danielftsilva/TS-808-Replica/KiCad Project/Layout/3D view.png

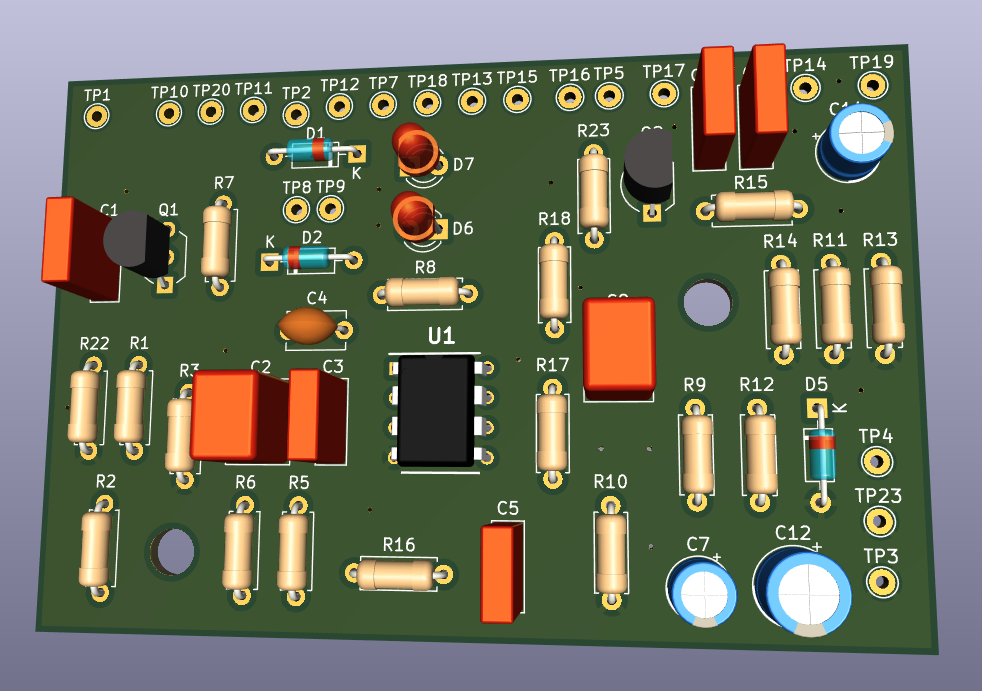
KiCad Project/Layout/3D view.png
