danielftsilva/TS-808-Replica/KiCad Project/Layout/Layout.png

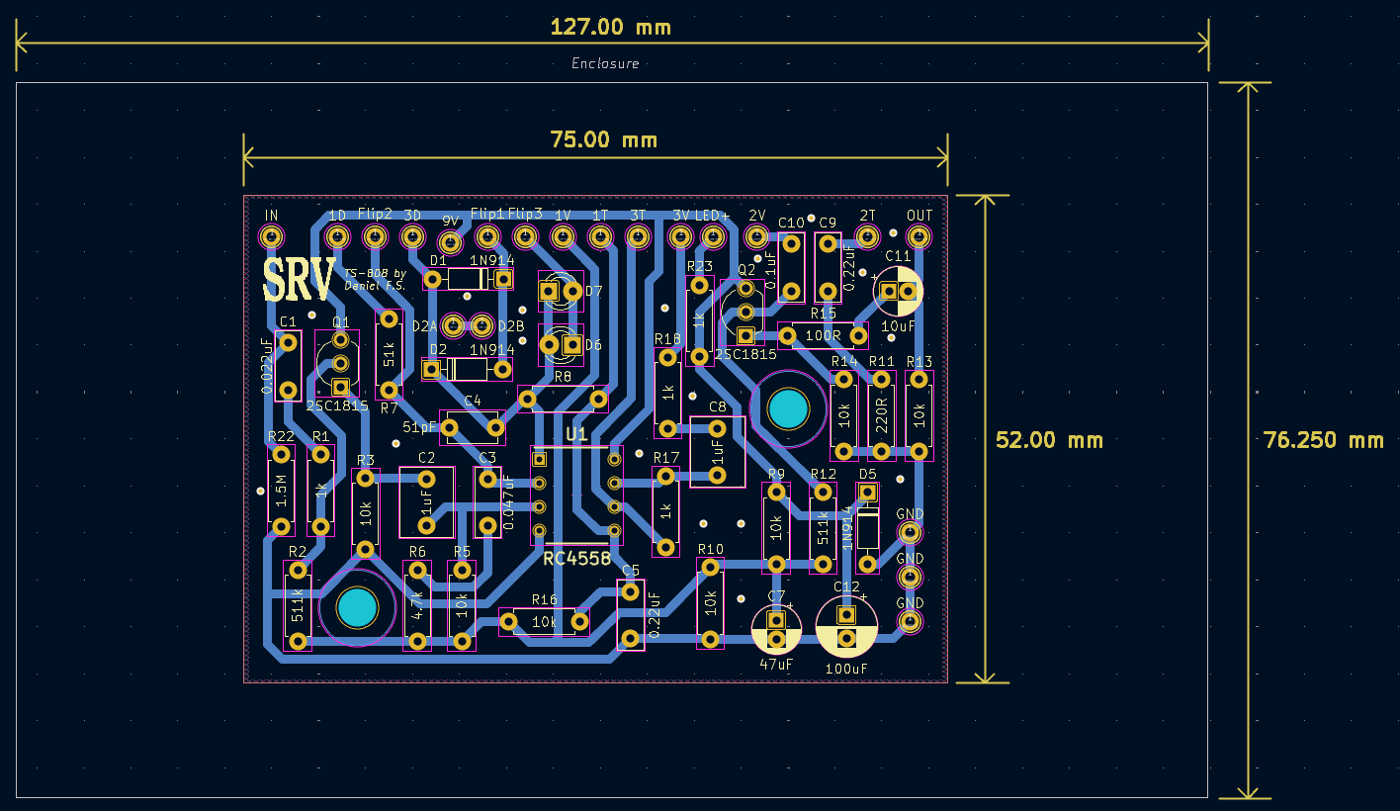
KiCad Project/Layout/Layout.png
