danielftsilva/TS-808-Replica/KiCad Project/Layout/Placement_1.png

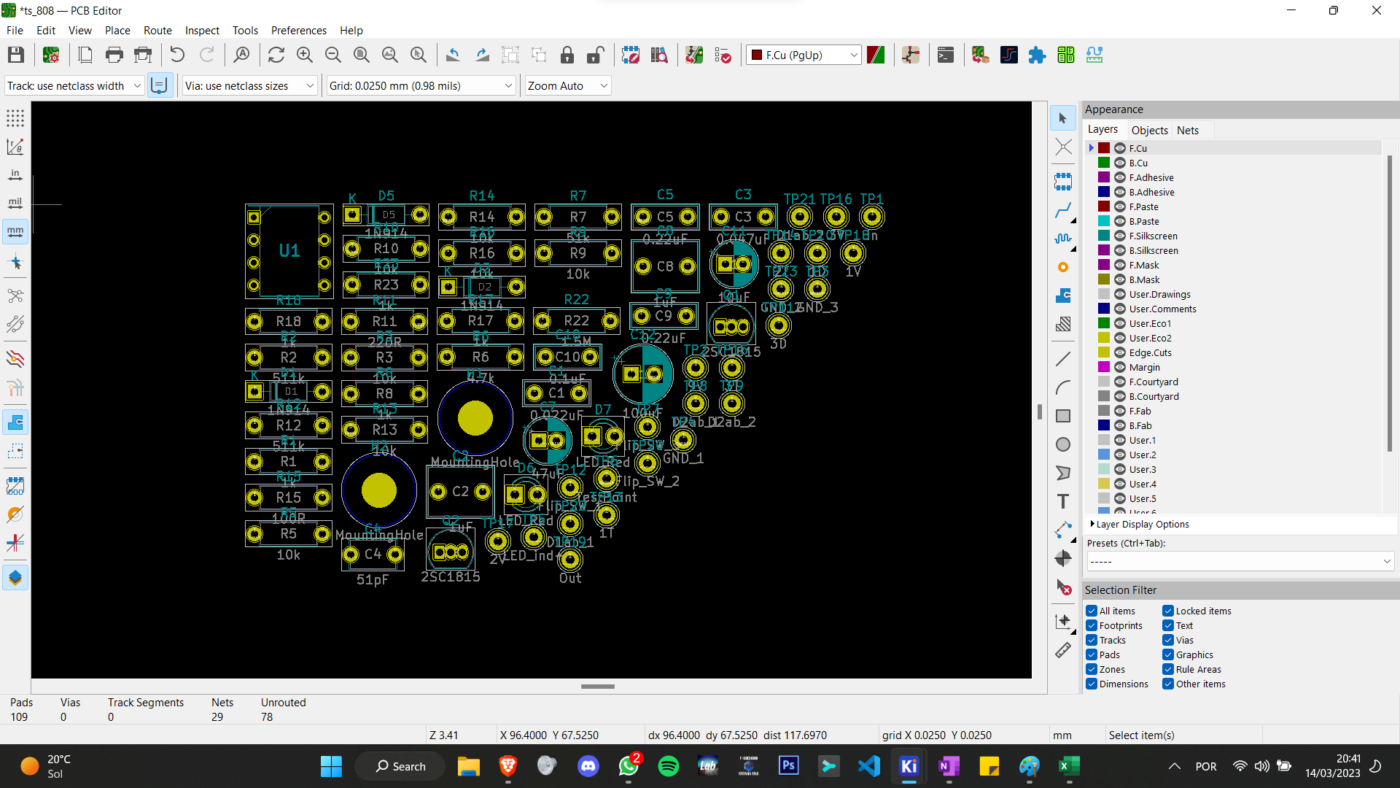
KiCad Project/Layout/Placement_1.png
