danielftsilva/TS-808-Replica/KiCad Project/Layout/Placement_2.png

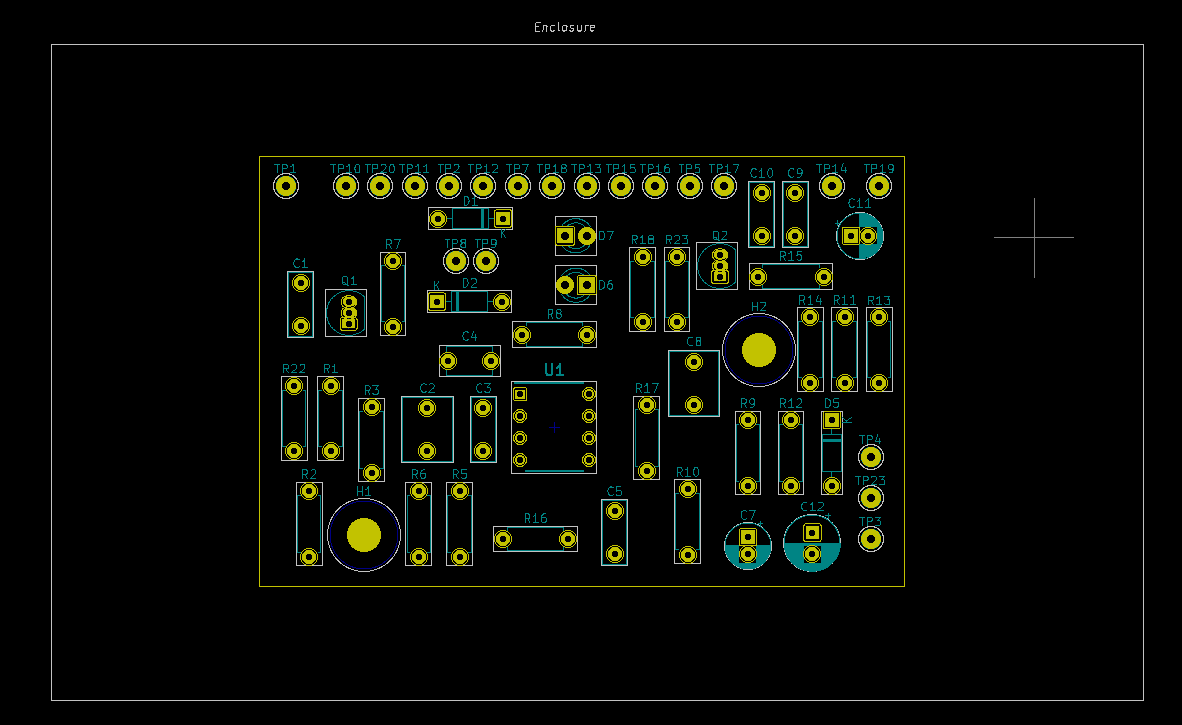
KiCad Project/Layout/Placement_2.png
