danielftsilva/TS-808-Replica/KiCad Project/Layout/tracks_1.png

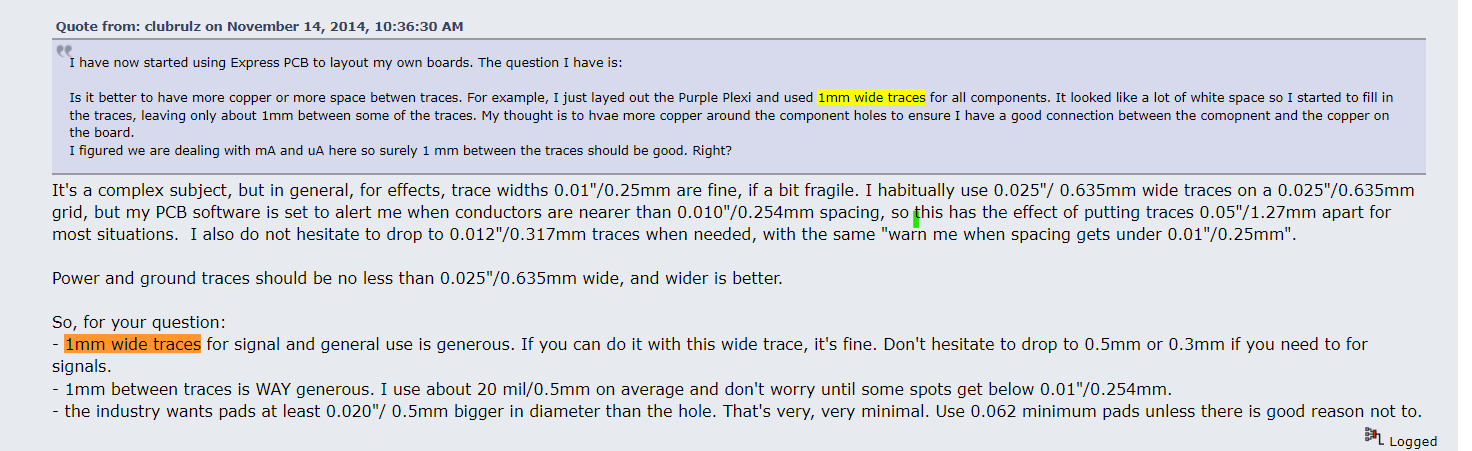
KiCad Project/Layout/tracks_1.png
