danielftsilva/TS-808-Replica/KiCad Project/Layout/tracks_2.png

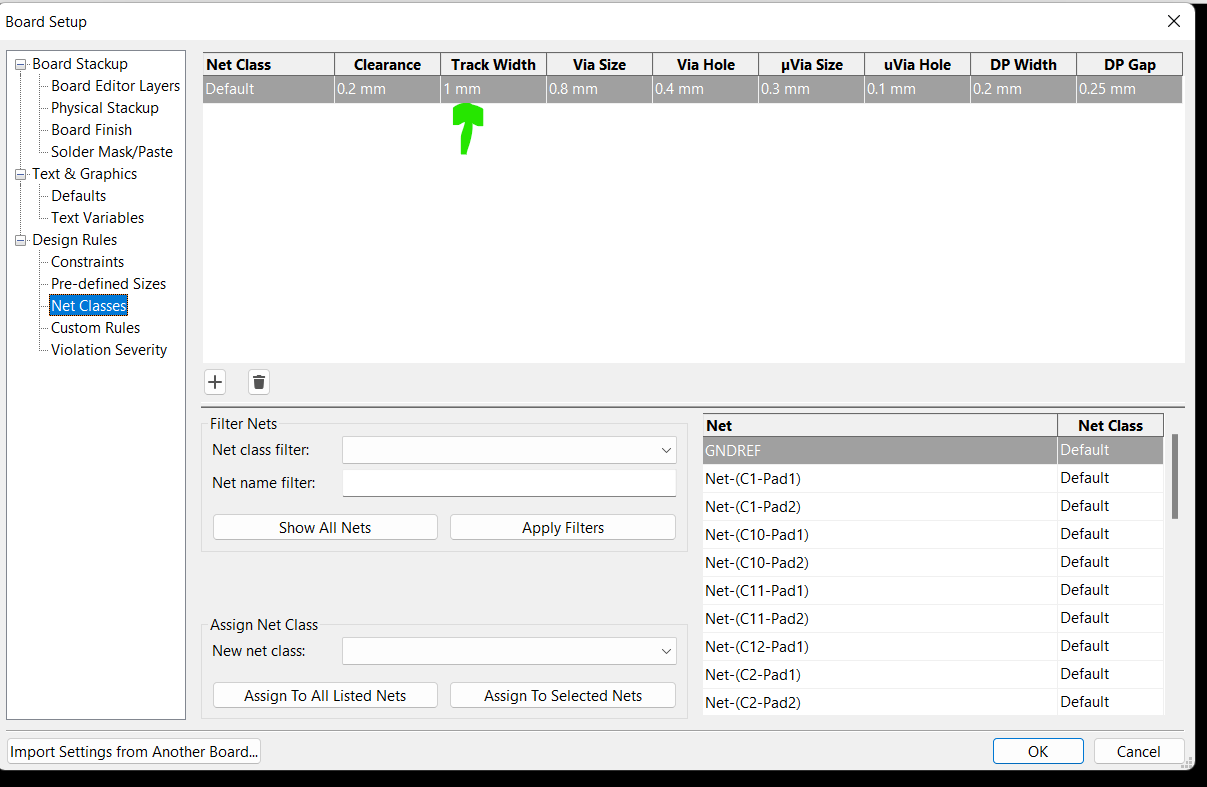
KiCad Project/Layout/tracks_2.png
