danielftsilva/TS-808-Replica/Assembly/PCB_populated.jpg

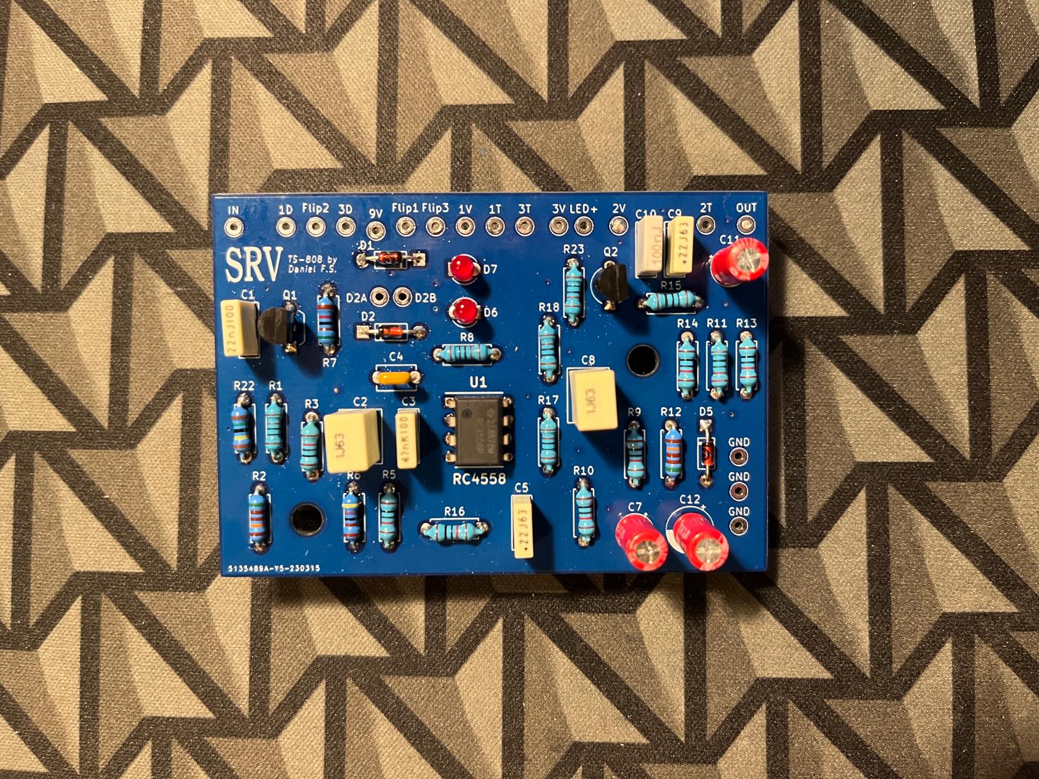
Assembly/PCB_populated.jpg
