danielftsilva/TS-808-Replica/Assembly/Pedal_assembled_2.jpeg

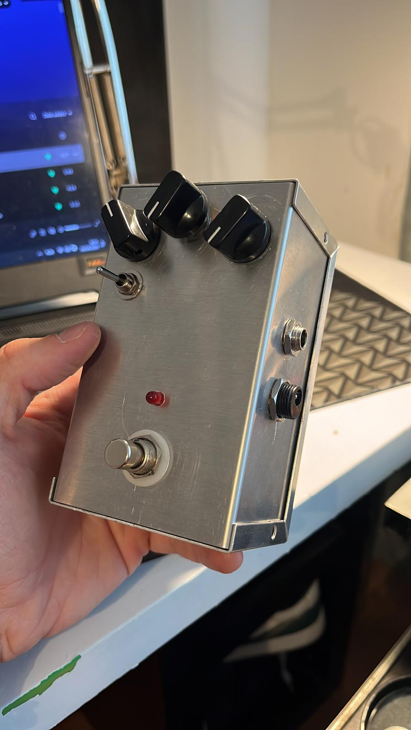
Assembly/Pedal_assembled_2.jpeg
