danielftsilva/TS-808-Replica/Assembly/Pedal_assembled_3.jpeg

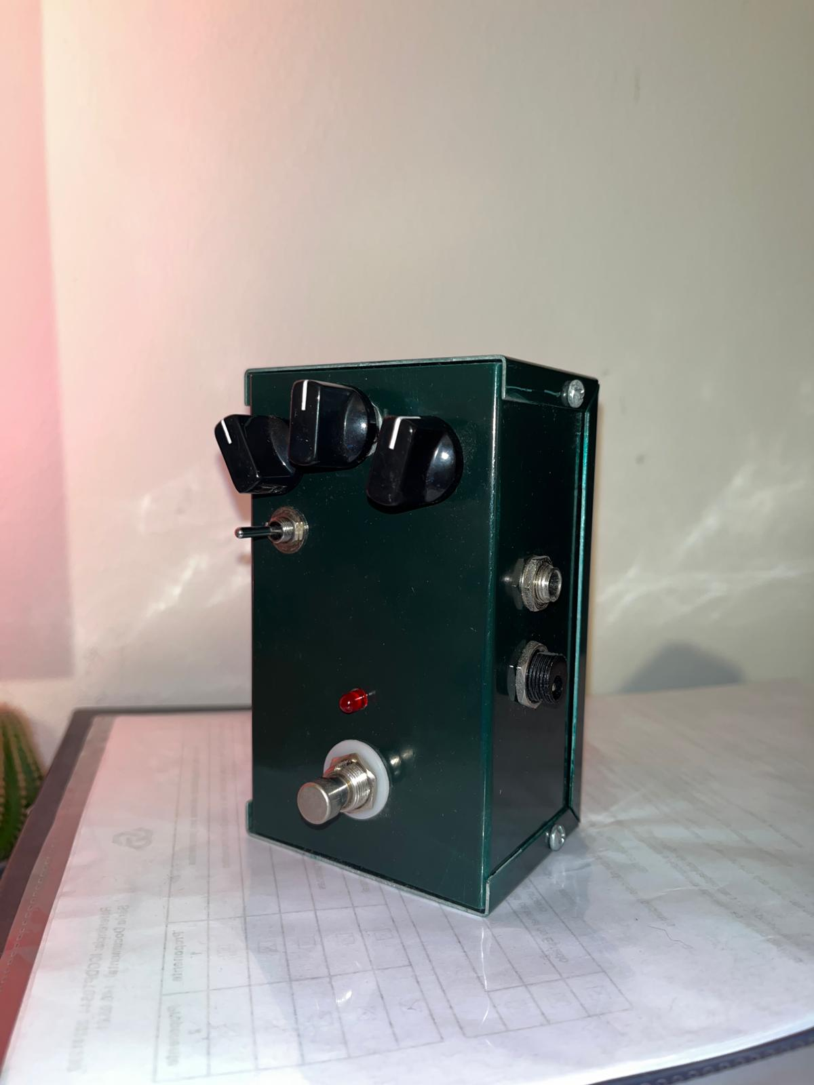
Assembly/Pedal_assembled_3.jpeg
