danielftsilva/TS-808-Replica/KiCad Project/production/JLCPCB_KiCad_board_setup_2.png

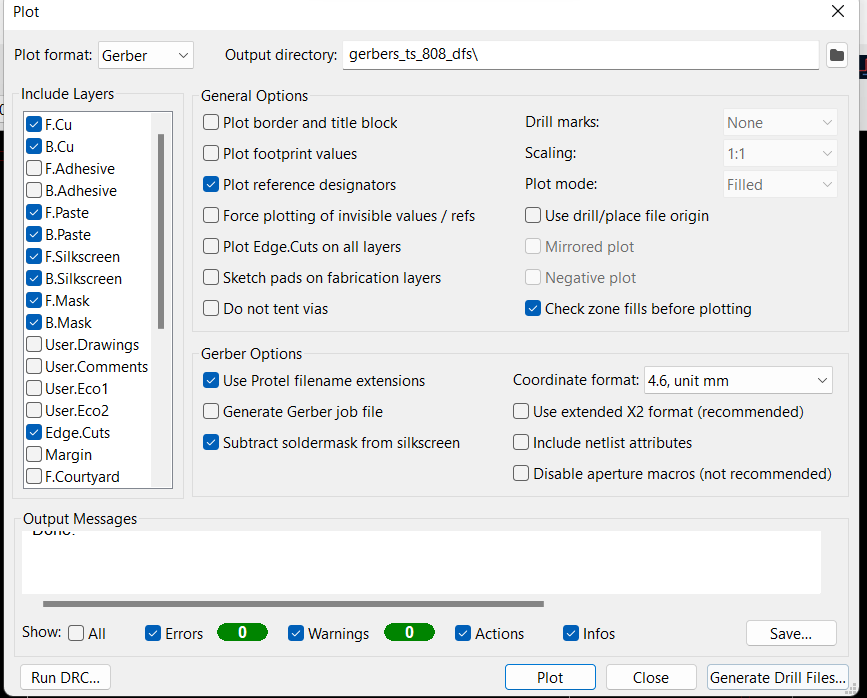
KiCad Project/production/JLCPCB_KiCad_board_setup_2.png
