danielftsilva/TS-808-Replica/Tests/Pedal_ON_1.jpeg

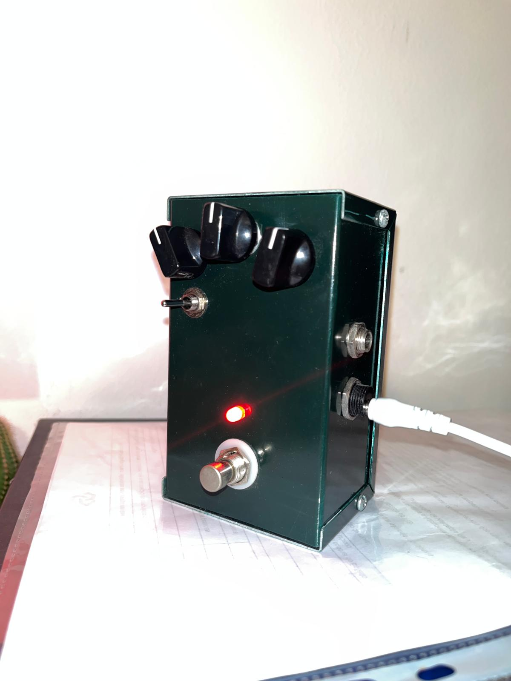
Tests/Pedal_ON_1.jpeg
