danielftsilva/TS-808-Replica/Tests/Pedal_ON_2.jpeg

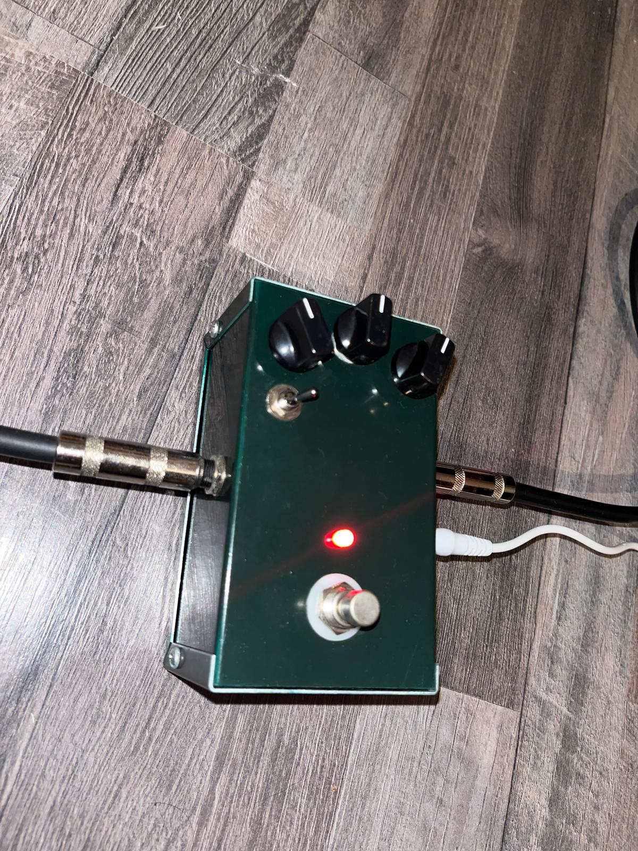
Tests/Pedal_ON_2.jpeg
