danielftsilva/TS-808-Replica/Tests/TROUBLESHOOTING CHART.jpg

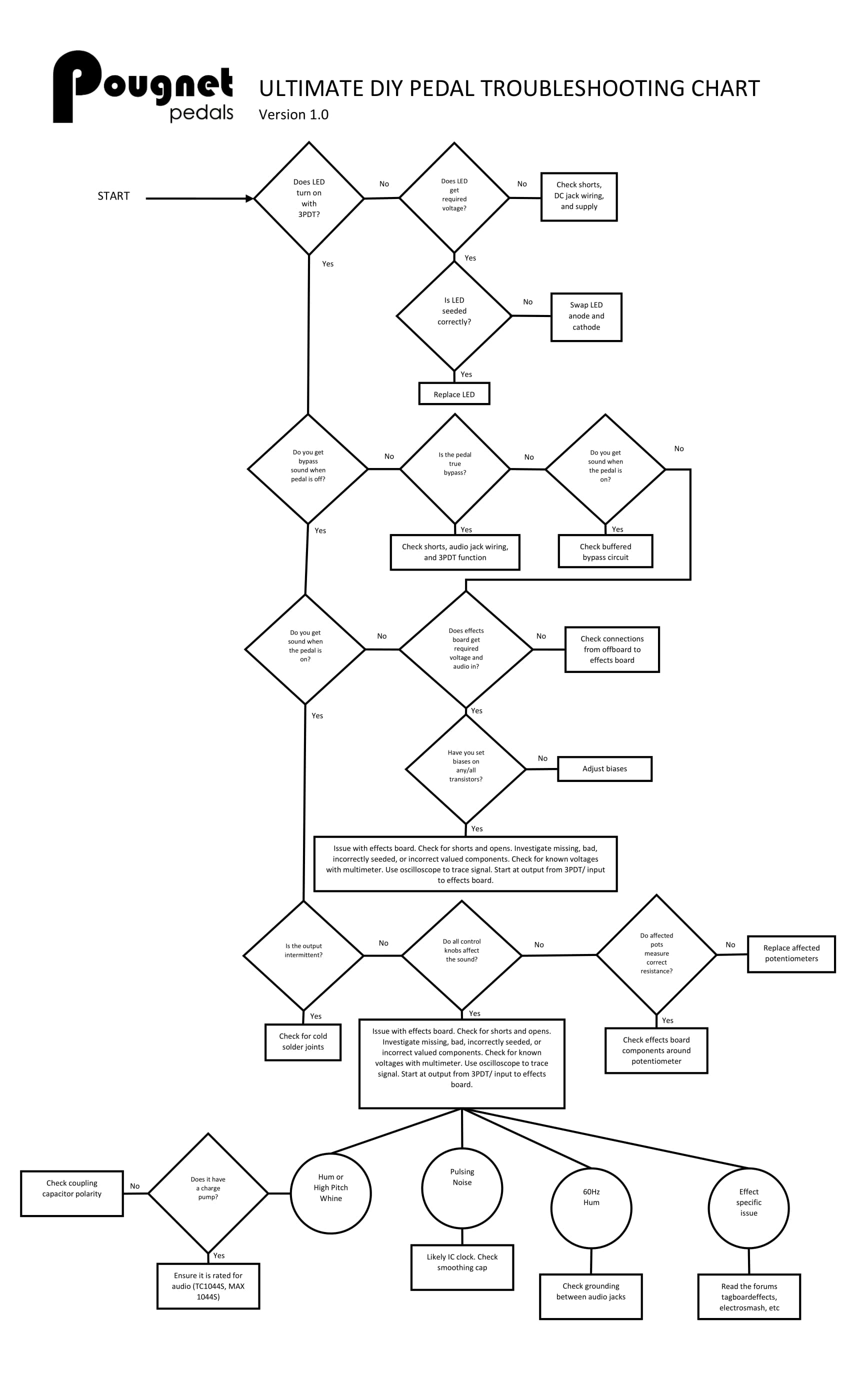
Tests/TROUBLESHOOTING CHART.jpg
